Mik0aj/3D-mouse/models/STL/encoderholder.stl

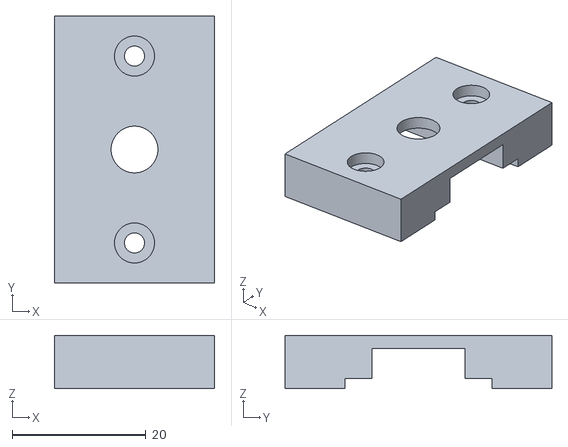
[picture p36: CAD file, 2023-01-20]
models/STL/encoderholder.stl
24.0 x 40.0 x 8.00
