Mik0aj/3D-mouse/models/STL/mouse-Knob.stl

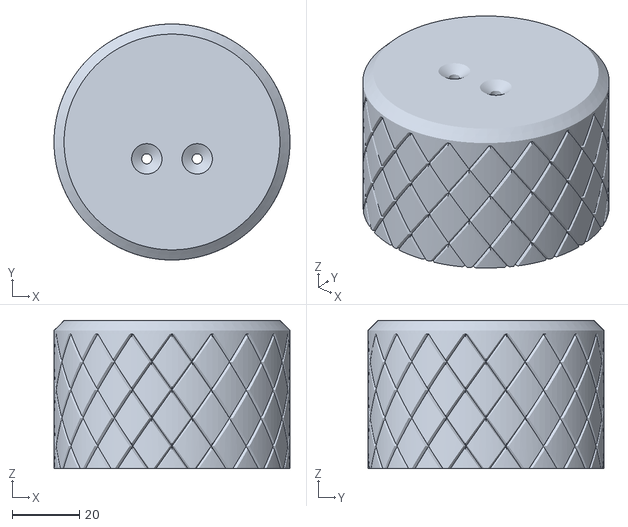
[picture p37: CAD file, 2023-01-20]
models/STL/mouse-Knob.stl
70.0 x 70.0 x 44.0
