Mik0aj/3D-mouse/models/STL/mouseXspring.stl

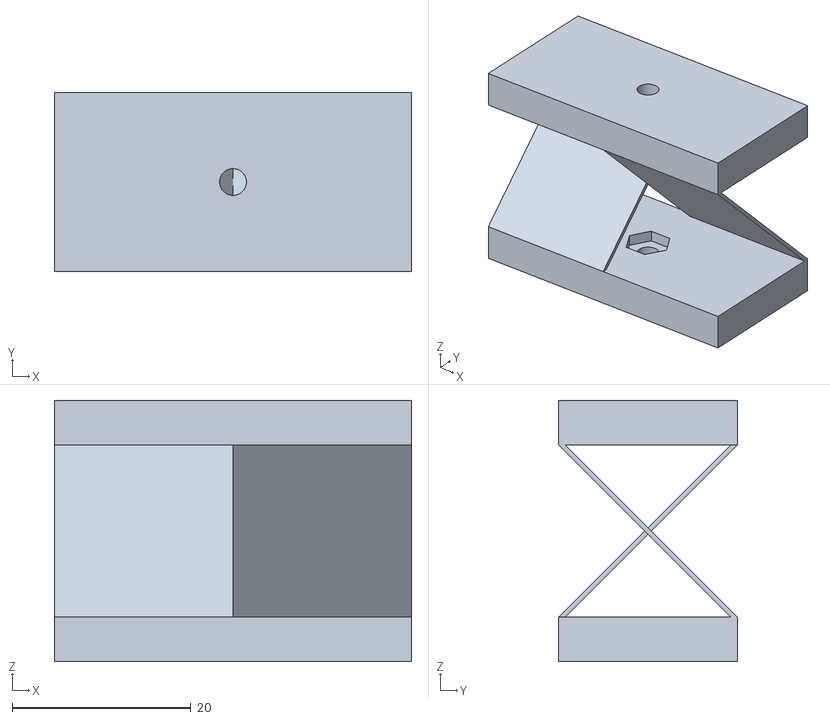
[picture p38: CAD file, 2023-01-20]
models/STL/mouseXspring.stl
40.0 x 20.0 x 29.3
