Mik0aj/3D-mouse/models/STL/mouseZspring.stl

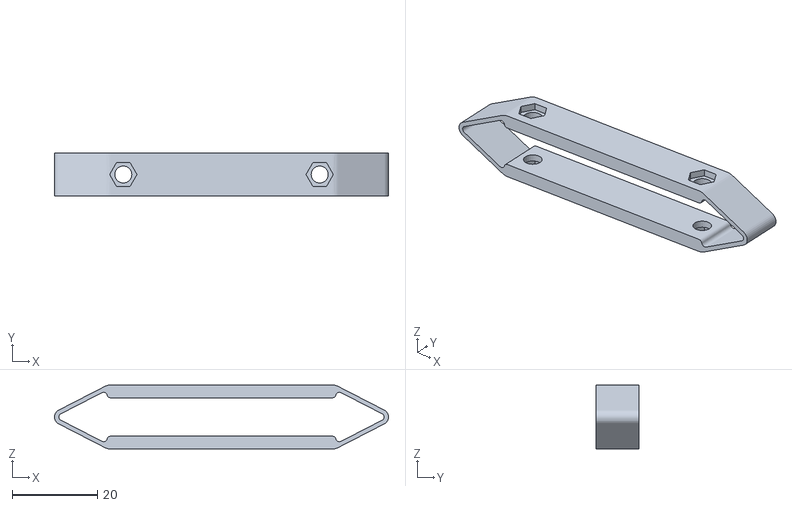
[picture p39: CAD file, 2022-06-18]
models/STL/mouseZspring.stl
78.3 x 10.0 x 15.0
