Mik0aj/3D-mouse/models/STL/mouseXspringHoleClip.stl

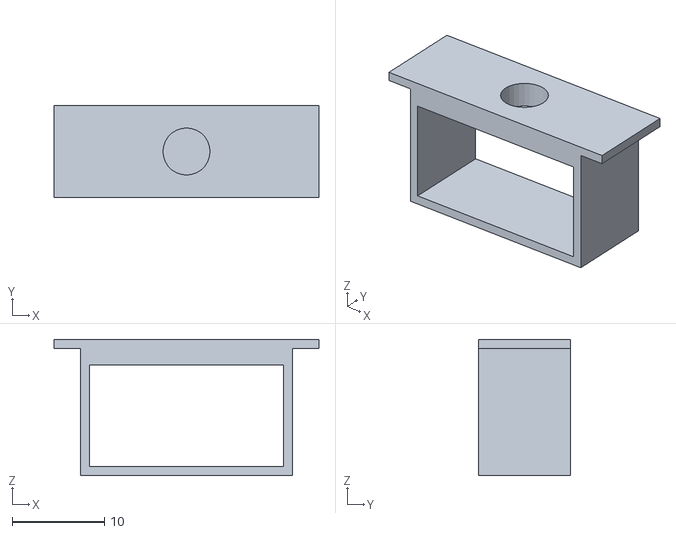
[picture p40: CAD file, 2022-06-18]
models/STL/mouseXspringHoleClip.stl
28.7 x 10.0 x 14.8
