Mik0aj/3D-mouse/models/STL/mouseXspringWithHole.stl

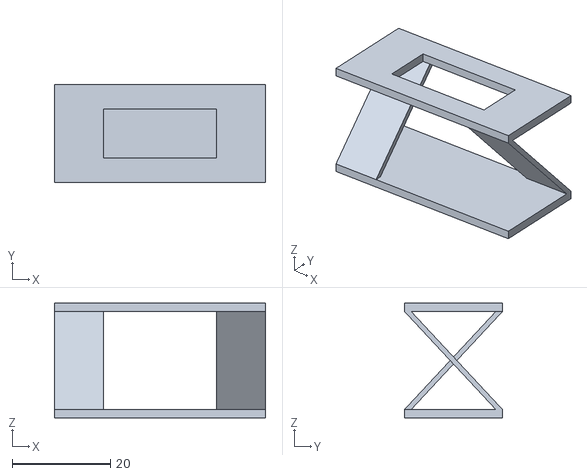
[picture p41: CAD file, 2022-06-18]
models/STL/mouseXspringWithHole.stl
43.0 x 20.0 x 23.4
