Mik0aj/3D-mouse/models/STL/mouseOrthoPlanarSpring.stl

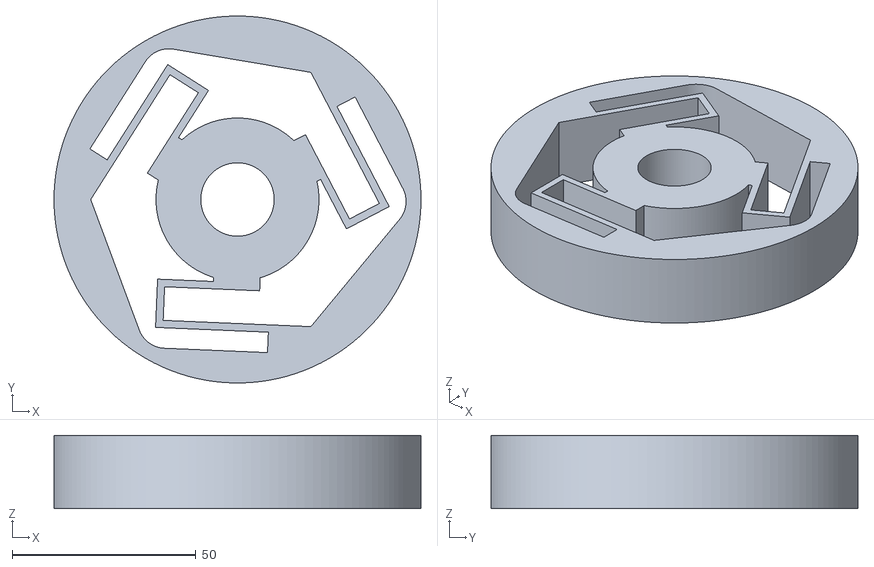
[picture p42: CAD file, 2022-04-02]
models/STL/mouseOrthoPlanarSpring.stl
100.0 x 100.0 x 20.0
