Mik0aj/3D-mouse/models/STL/arduinoGloveTopPad.stl

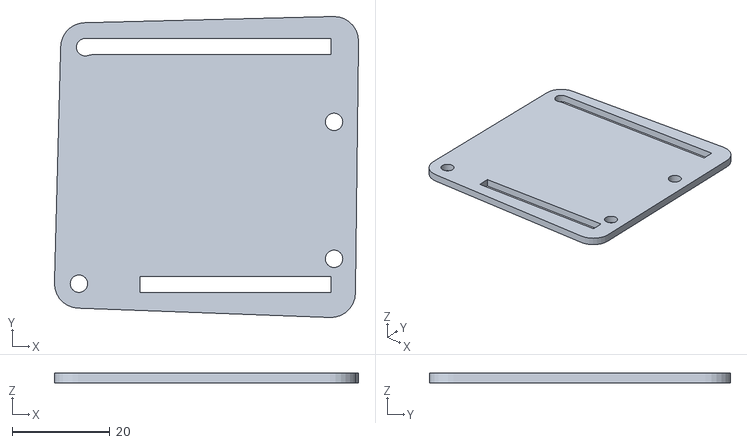
[picture p43: CAD file, 2022-03-31]
models/STL/arduinoGloveTopPad.stl
62.1 x 61.4 x 2.00
