Mik0aj/3D-mouse/models/STL/arduinoGloveSpacer.stl

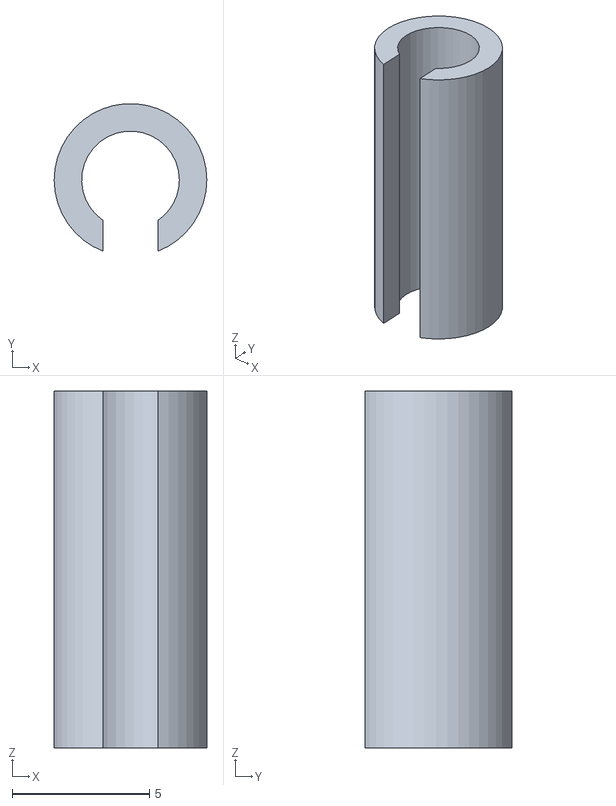
[picture p44: CAD file, 2022-03-31]
models/STL/arduinoGloveSpacer.stl
5.56 x 5.37 x 13.0
