Mik0aj/3D-mouse/models/STL/arduinoGloveBottomPad.stl

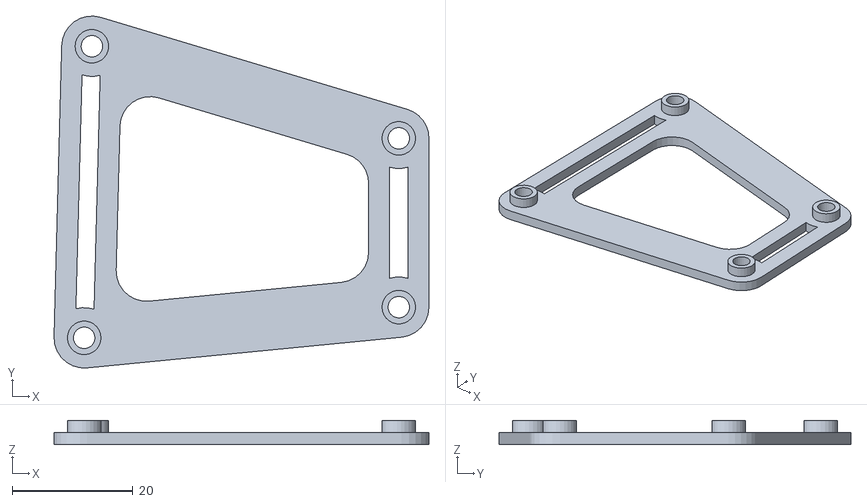
[picture p45: CAD file, 2022-03-31]
models/STL/arduinoGloveBottomPad.stl
62.1 x 58.2 x 4.00
