Mik0aj/3D-mouse/code/VsCodeProject/src/XInputAdapter.cpp

// #include <XInputAdapter.h>

// void XInputAdapter::setXYZ(int index, long value)
// {
//     switch (index)
//     {
//     case 0:
//         XInput.setJoystickX(JOY_LEFT, value, false);
//         break;
//     case 1:
//         XInput.setJoystickY(JOY_LEFT, value, false);
//         break;
//     case 2:
// //        XInput.setTrigger(TRIGGER_LEFT, value);
//         break;
//     default:
//         break;
//     }
// }

// void XInputAdapter::setRXRYRZ(int index, long value)
// {
//     switch (index)
//     {
//     case 0:
//         XInput.setJoystickX(JOY_RIGHT, value, false);
//         break;
//     case 1:
//         XInput.setJoystickY(JOY_RIGHT, value, false);
//         break;
//     case 2:
// //        XInput.setTrigger(TRIGGER_RIGHT, value);
//         break;
//     default:
//         break;
//     }
// }

// void XInputAdapter::begin()
// {
//     XInput.begin();
// }

// void XInputAdapter::send()
// {
//     XInput.send();
// }

// void XInputAdapter::setXAxisRange(int MIN_X, int MAX_X)
// {
//     XInput.setRange(JOY_LEFT, MIN_X, MAX_X);
// }
// void XInputAdapter::setYAxisRange(int MIN_X, int MAX_X)
// {
//     XInput.setRange(JOY_LEFT, MIN_X, MAX_X);
// }
// void XInputAdapter::setZAxisRange(int MIN_X, int MAX_X)
// {
//     XInput.setRange(TRIGGER_LEFT, MIN_X, MAX_X);
// }

// void XInputAdapter::setRxAxisRange(int MIN_X, int MAX_X)
// {
//     XInput.setRange(JOY_RIGHT, MIN_X, MAX_X);
// }
// void XInputAdapter::setRyAxisRange(int MIN_X, int MAX_X)
// {
//     XInput.setRange(JOY_RIGHT, MIN_X, MAX_X);
// }
// void XInputAdapter::setRzAxisRange(int MIN_X, int MAX_X)
// {
//     XInput.setRange(TRIGGER_RIGHT, MIN_X, MAX_X);
// }
